mfoster0/DataVis-GrpProj/Assets/Flowchart/flowchart.jpg

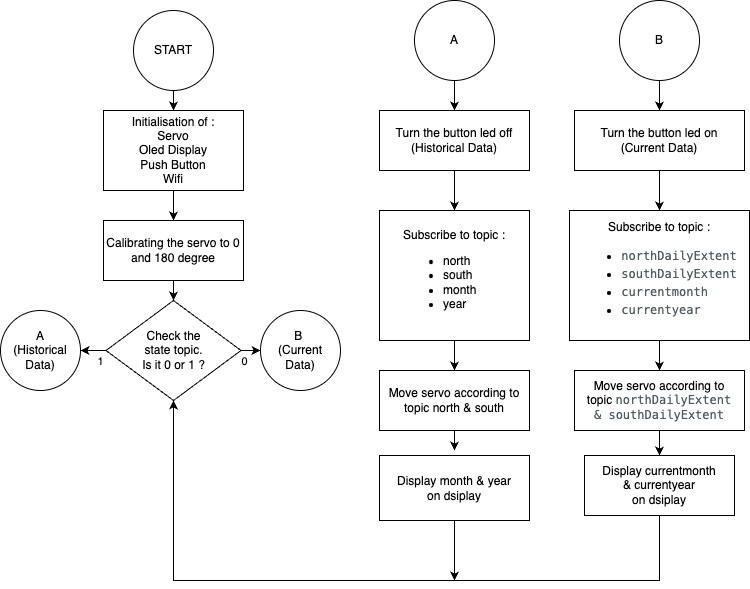
Assets/Flowchart/flowchart.jpg
