mfoster0/DataVis-GrpProj/Assets/Flowchart/Untitled Diagram (1).jpg

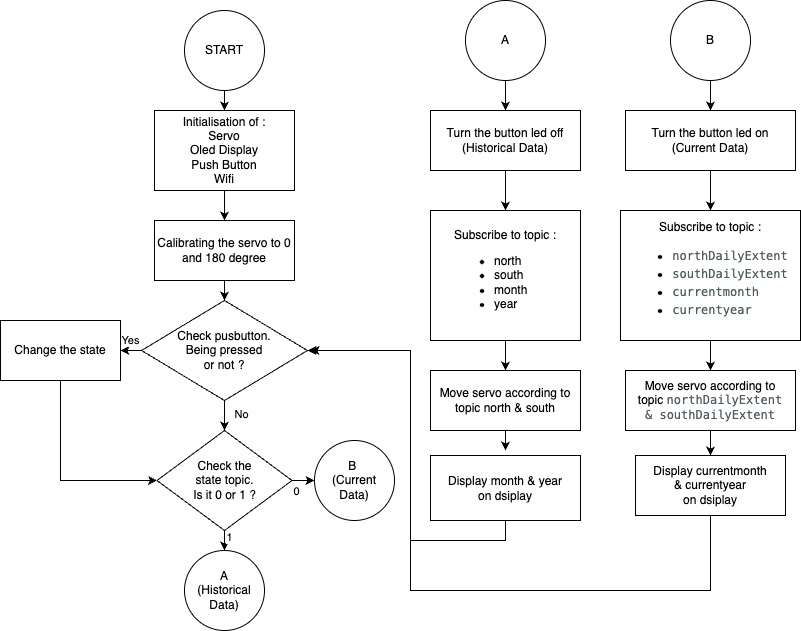
Assets/Flowchart/Untitled Diagram (1).jpg
