mfoster0/DataVis-GrpProj/Unity/Assets/Plugins/CW/LeanCommon/Examples/Textures/Plus.png

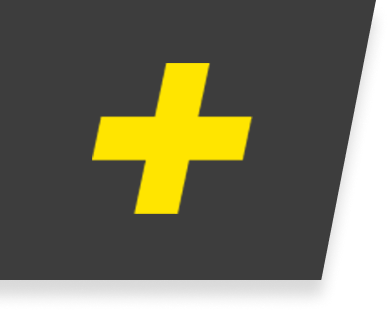
Unity/Assets/Plugins/CW/LeanCommon/Examples/Textures/Plus.png
