mfoster0/DataVis-GrpProj/Unity/Assets/Plugins/CW/LeanTouch/Examples/Textures/ArrowCurve.png

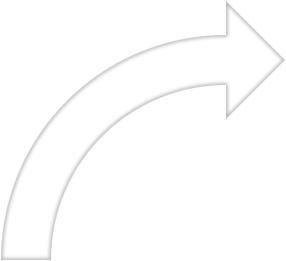
Unity/Assets/Plugins/CW/LeanTouch/Examples/Textures/ArrowCurve.png
