mfoster0/DataVis-GrpProj/Unity/Assets/Plugins/CW/LeanTouch/Examples/Textures/ArrowStraight.png

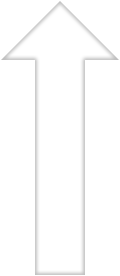
Unity/Assets/Plugins/CW/LeanTouch/Examples/Textures/ArrowStraight.png
