mfoster0/DataVis-GrpProj/Unity/Assets/Plugins/CW/LeanTouch/Examples/Textures/ArrowTwist.png

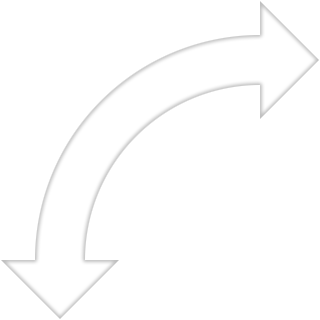
Unity/Assets/Plugins/CW/LeanTouch/Examples/Textures/ArrowTwist.png
