mfoster0/DataVis-GrpProj/Unity/Assets/Plugins/CW/LeanTouch/Examples/Textures/Circle.png

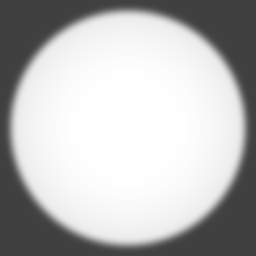
Unity/Assets/Plugins/CW/LeanTouch/Examples/Textures/Circle.png
