mfoster0/DataVis-GrpProj/Unity/Assets/Plugins/CW/LeanTouch/Examples/Textures/GlowingDot.png

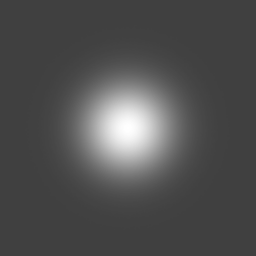
Unity/Assets/Plugins/CW/LeanTouch/Examples/Textures/GlowingDot.png
