mfoster0/DataVis-GrpProj/Unity/Assets/Plugins/CW/LeanTouch/Examples/Textures/GlowingTrail.png

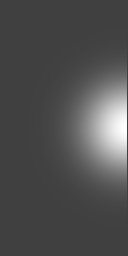
Unity/Assets/Plugins/CW/LeanTouch/Examples/Textures/GlowingTrail.png
