mfoster0/DataVis-GrpProj/Unity/Assets/Plugins/CW/Shared/Common/Examples/Textures/DemoDescription.png

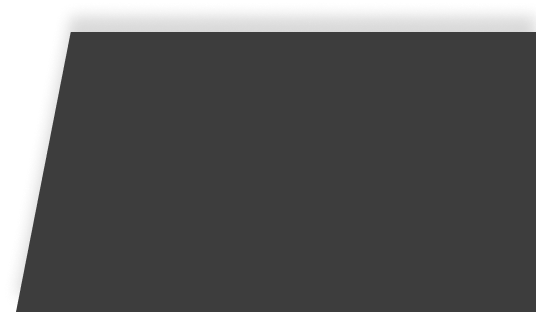
Unity/Assets/Plugins/CW/Shared/Common/Examples/Textures/DemoDescription.png
