mfoster0/DataVis-GrpProj/Unity/Assets/Plugins/CW/Shared/Common/Examples/Textures/DemoLeft.png

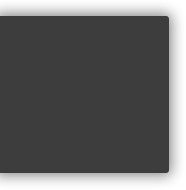
Unity/Assets/Plugins/CW/Shared/Common/Examples/Textures/DemoLeft.png
