mfoster0/DataVis-GrpProj/Unity/Assets/ExampleAssets/Tutorial/Images/1-welcome-screen-image.png

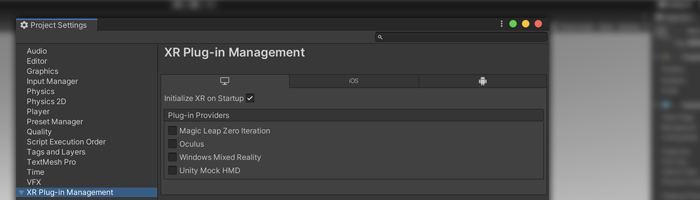
Unity/Assets/ExampleAssets/Tutorial/Images/1-welcome-screen-image.png
