mfoster0/DataVis-GrpProj/Unity/Assets/ExampleAssets/Tutorial/Images/project-header-ar.png

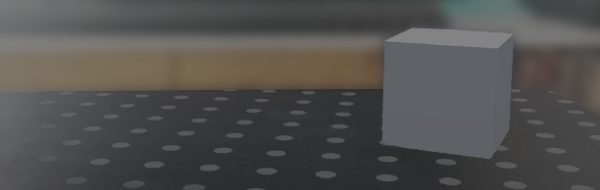
Unity/Assets/ExampleAssets/Tutorial/Images/project-header-ar.png
