mfoster0/DataVis-GrpProj/Unity/Assets/ice_gauge_dial_rev.fbm/scale_fix v2.png

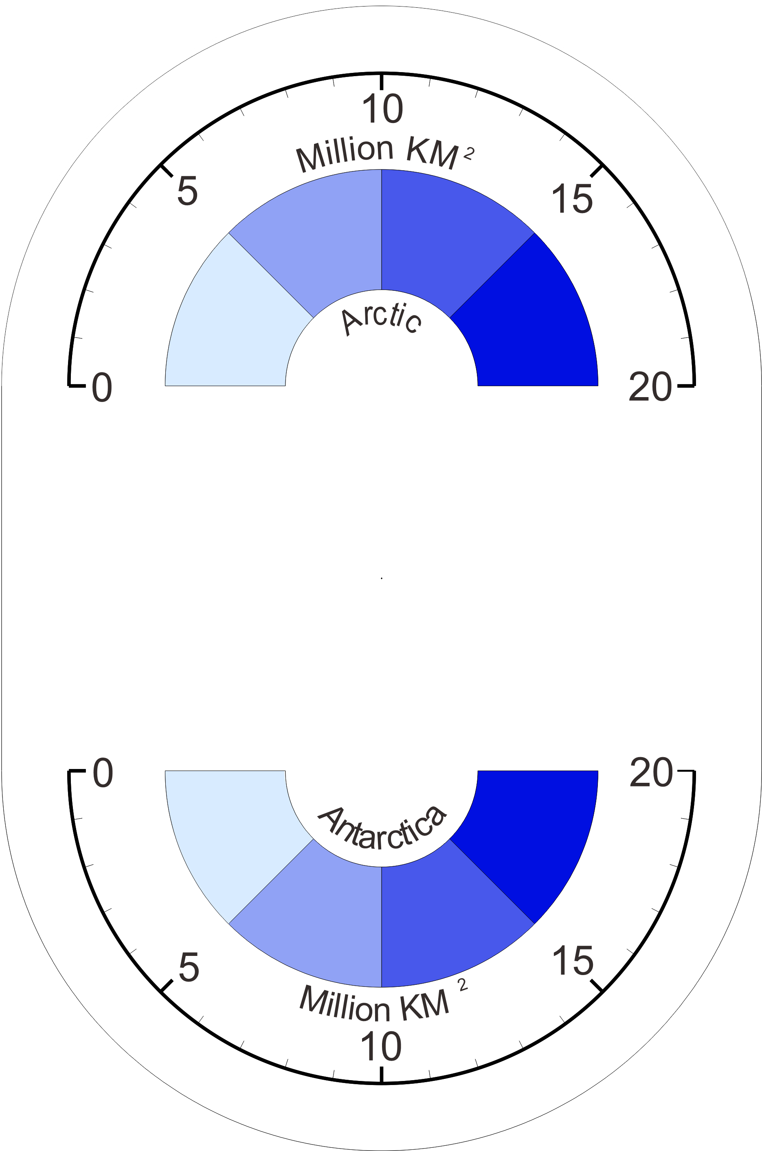
Unity/Assets/ice_gauge_dial_rev.fbm/scale_fix v2.png
